kshitijl/attiny-ir-remote/progress-pics/2016-12-10 04.19.34.jpg

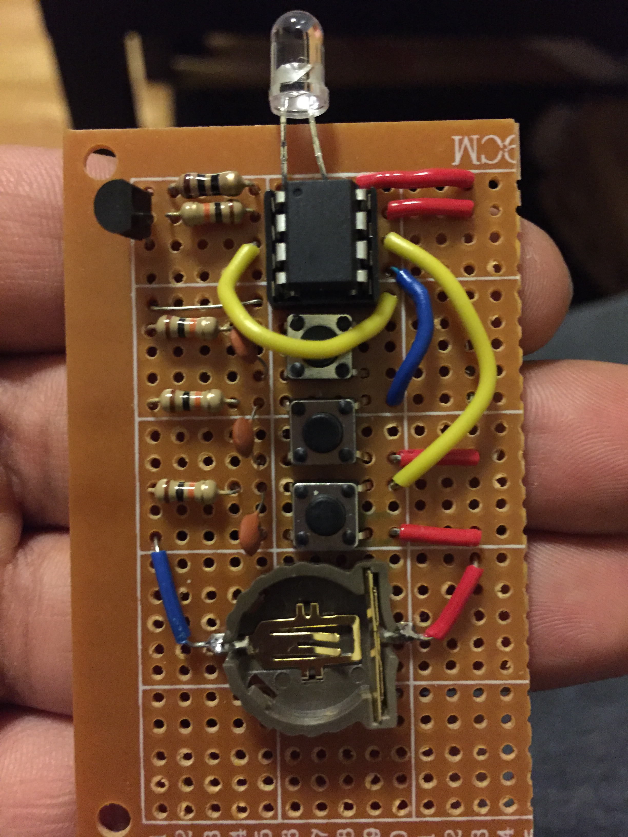
progress-pics/2016-12-10 04.19.34.jpg
