kshitijl/attiny-ir-remote/progress-pics/2017-08-01 23.06.16.jpg

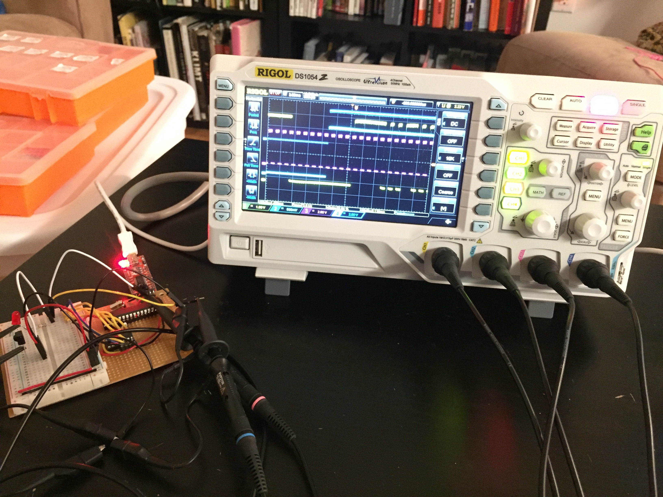
progress-pics/2017-08-01 23.06.16.jpg
