kshitijl/attiny-ir-remote/progress-pics/2017-08-05 11.24.27.jpg

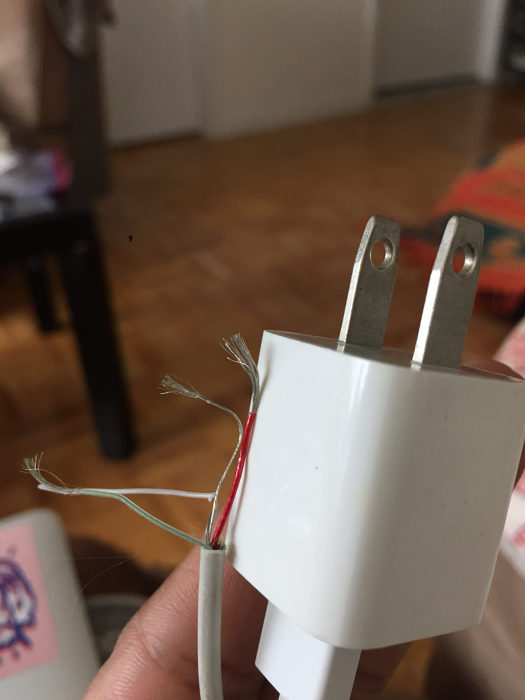
progress-pics/2017-08-05 11.24.27.jpg
