kshitijl/attiny-ir-remote/progress-pics/2017-08-05 15.10.06.jpg

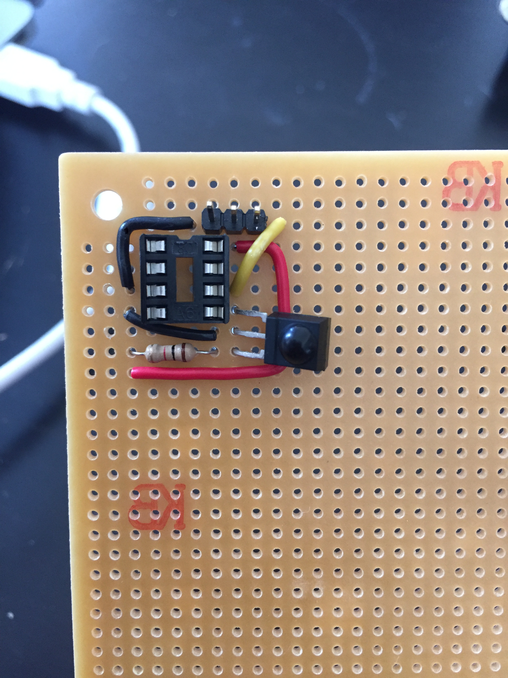
progress-pics/2017-08-05 15.10.06.jpg
