kshitijl/attiny-ir-remote/progress-pics/2017-08-05 15.44.11.jpg

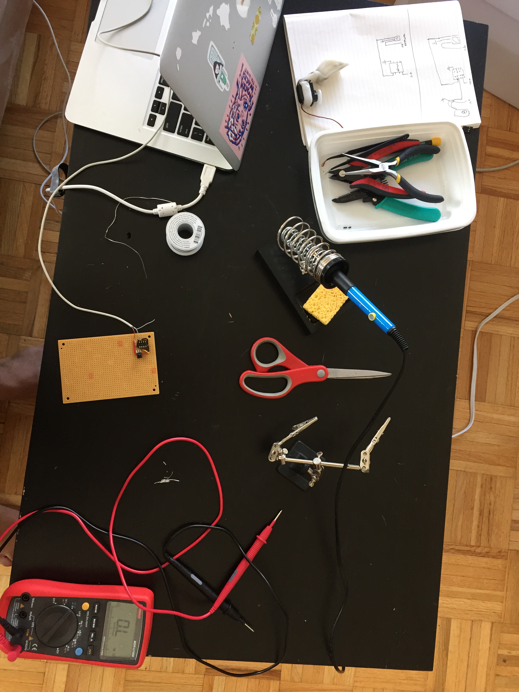
progress-pics/2017-08-05 15.44.11.jpg
