kshitijl/attiny-ir-remote/progress-pics/2017-08-05 16.09.07.jpg

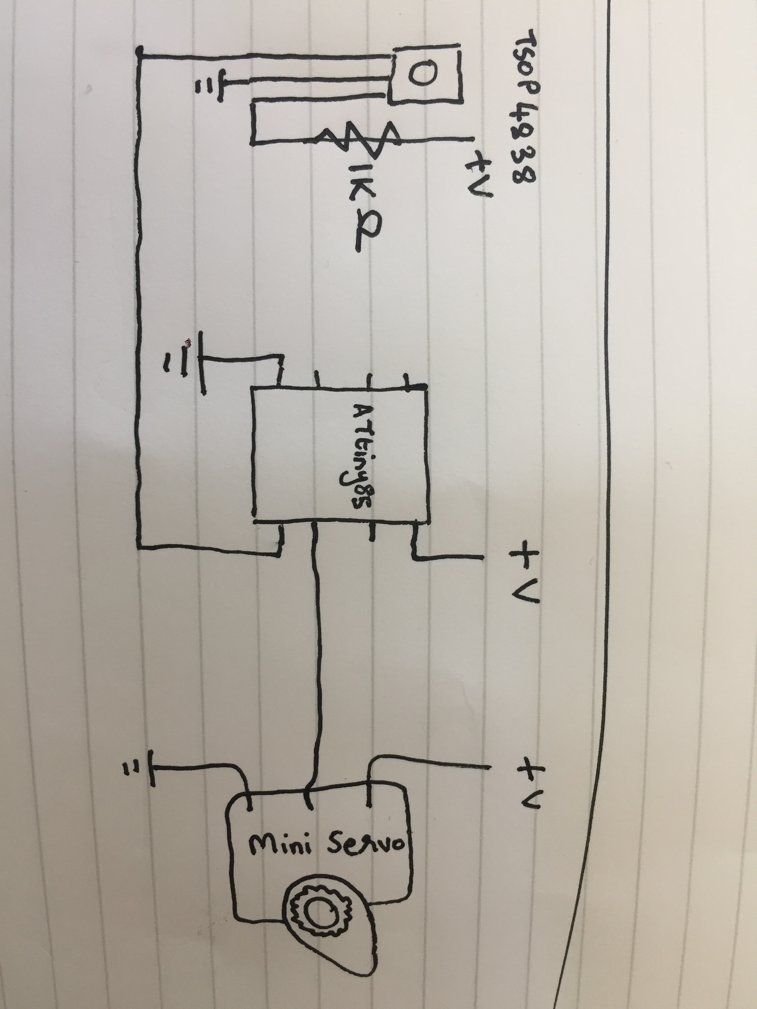
progress-pics/2017-08-05 16.09.07.jpg
