kshitijl/attiny-ir-remote/progress-pics/2017-08-05 16.20.30.jpg

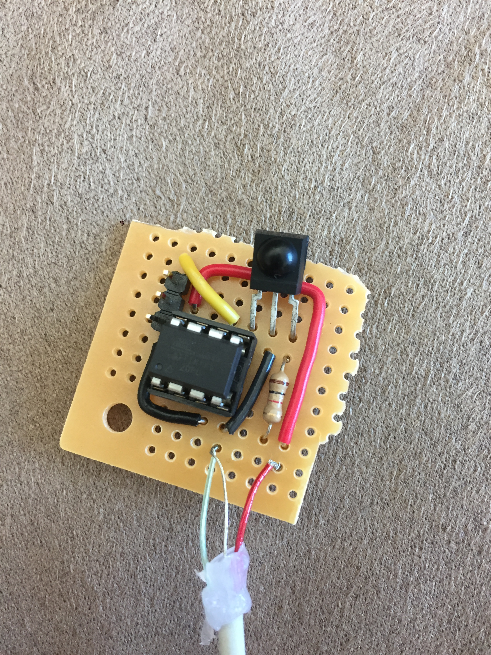
progress-pics/2017-08-05 16.20.30.jpg
