kshitijl/attiny-ir-remote/progress-pics/2017-08-05 16.40.24.jpg

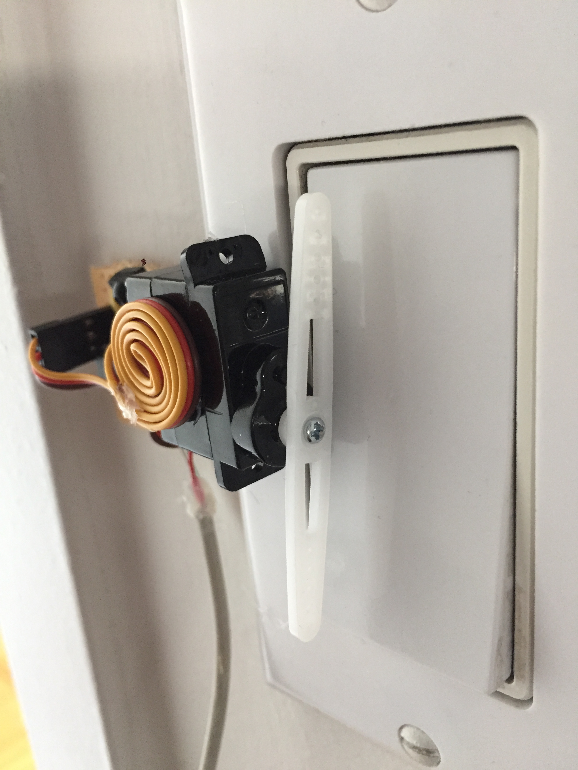
progress-pics/2017-08-05 16.40.24.jpg
