kshitijl/attiny-ir-remote/progress-pics/2017-08-05 16.42.45.jpg

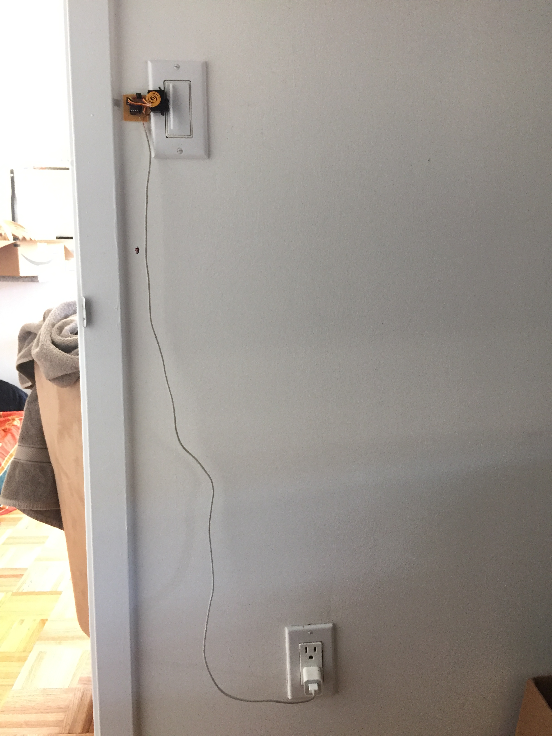
progress-pics/2017-08-05 16.42.45.jpg
