kshitijl/attiny-ir-remote/scope-traces/ir-packets-from-LG-remote/power-button.3.png

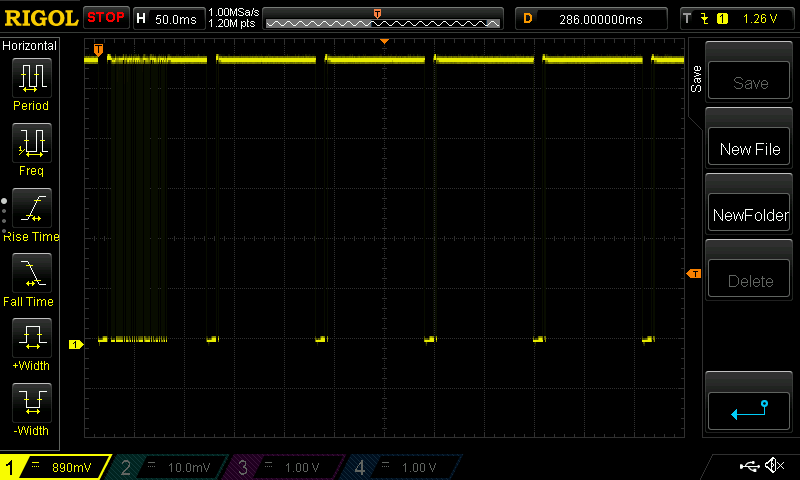
scope-traces/ir-packets-from-LG-remote/power-button.3.png
