kshitijl/attiny-ir-remote/scope-traces/ir-packets-from-LG-remote/power-button.png

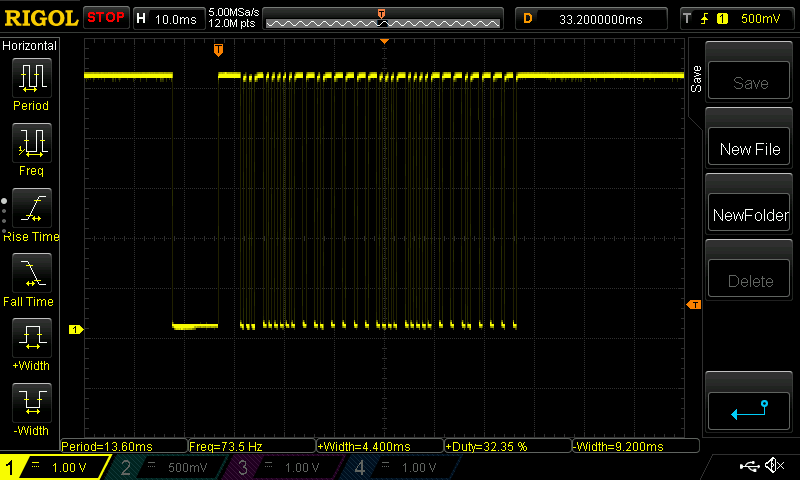
scope-traces/ir-packets-from-LG-remote/power-button.png
