kshitijl/attiny-ir-remote/scope-traces/pwm-for-servo/angle-5.png

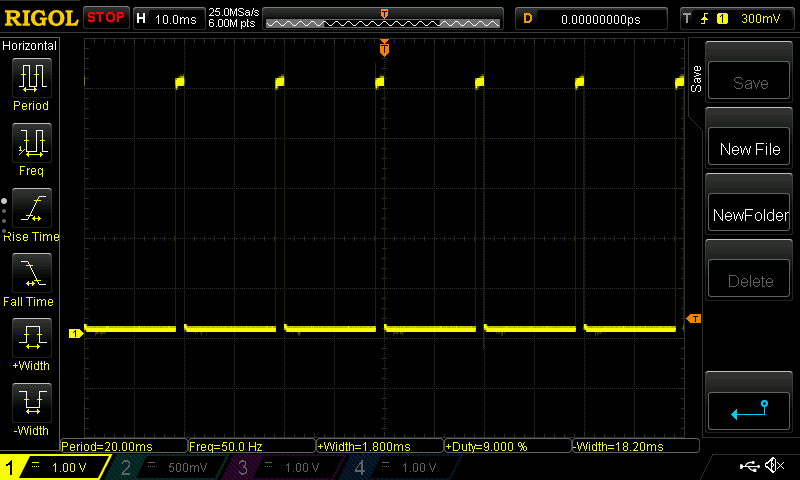
scope-traces/pwm-for-servo/angle-5.png
