kshitijl/attiny-ir-remote/scope-traces/pwm-for-servo/angle-20.png

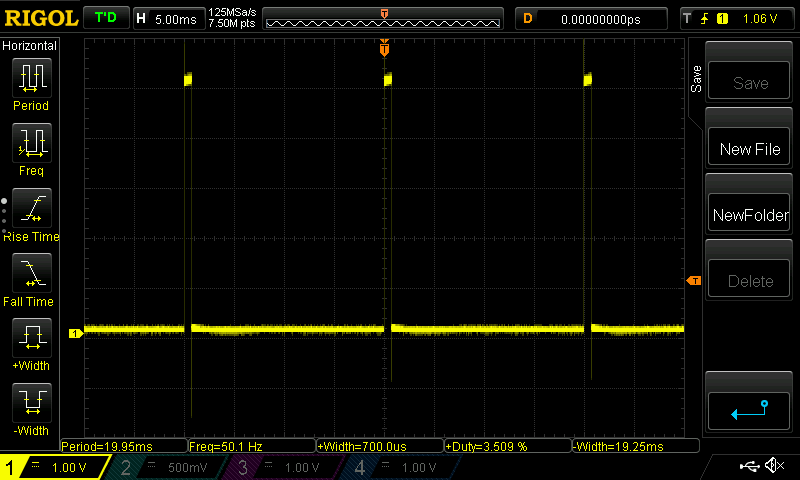
scope-traces/pwm-for-servo/angle-20.png
