kshitijl/attiny-ir-remote/scope-traces/pwm-for-servo/angle-100.png

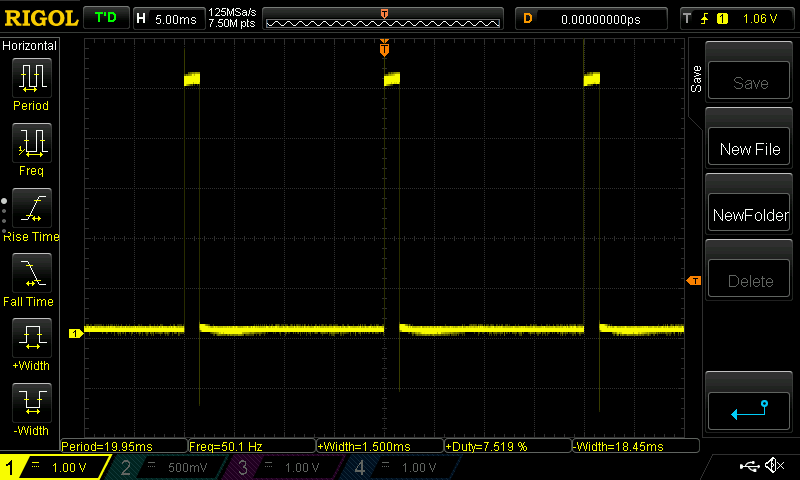
scope-traces/pwm-for-servo/angle-100.png
