kshitijl/attiny-ir-remote/scope-traces/pwm-for-servo/angle-140.png

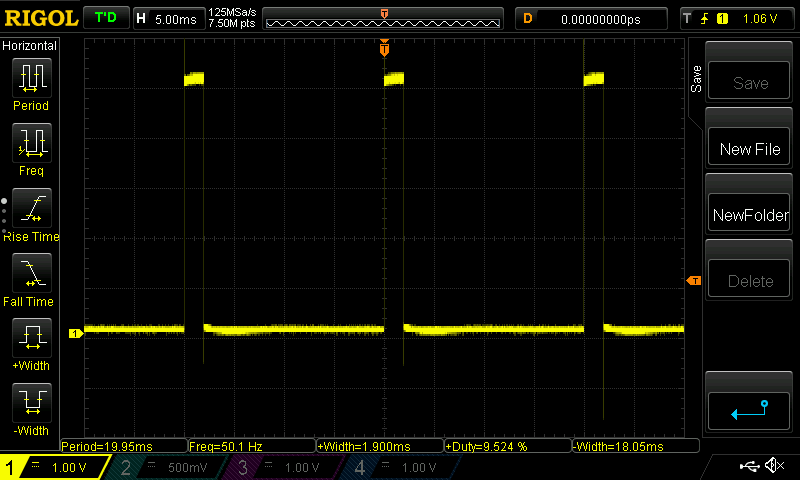
scope-traces/pwm-for-servo/angle-140.png
