kshitijl/attiny-ir-remote/pwm-attiny85.c

#include <avr/io.h>
#include <avr/interrupt.h>
#include <util/delay.h>

/*
  Don't do this.

  Just compute a max_duty and a min_duty and work in that space.

  No need for error-prone calculations where I have to think carefully
  about truncation at every step.
*/
uint8_t angle_to_OCR0B(uint8_t angle) {
  uint16_t initial = 2410;
  uint16_t slope = 52;
  initial += slope * angle;
  initial /= 1000;
  uint16_t answer = initial*OCR0A/100;
  return answer;
}

int main (void)
{
  // set pin 6/PB1/OC0B to be output
  // Timer/Counter0 Compare Match  output
	DDRB = (1 << DDB1);

  // Table 11-5. Select fast PWM with a prescaler of 256. In mode 7
  // (fast PWM with TOP = OCRA), OCR0A is the TOP value and you can
  // only get a PWM on OC0B. Why would you want that? To control the
  // frequency as well as duty cycle.
  TCCR0A = (1 << COM0B1) | (1 << WGM00) | (1 << WGM01);
  TCCR0B = (1 << CS02)   | (1 << WGM02);

  // In mode 7, TCNT0 counts from 0 to OCR0A for a complete PWM cycle.
  // We want the time period to be 20ms.
  // OCR0A * tick_period = 20ms
  // OCR0A = 20ms/tick_period_in_ms = 20ms * tick_frequency_in_1000Hz
  // OCR0A = 20ms * (1000 KHz / 256)
  // OCR0A = 20 * F_CPU / 256000

  OCR0A = 20 * F_CPU / 256000;

  const int lower = 20, upper = 100;
  
  while (1) {
    for(int angle = lower; angle < upper; ++angle) {
      OCR0B = angle_to_OCR0B(angle);
      _delay_ms(10);
    }
    //_delay_ms(1000);
    for(int angle = upper; angle > lower; --angle) {
      OCR0B = angle_to_OCR0B(angle);
      _delay_ms(10);
    }
  }
 
  return 0;
}
